robotsrulz/SP_Adapter/Inc/eeprom.h

/**
  ******************************************************************************
  * @file    EEPROM_Emulation/inc/eeprom.h 
  * @author  MCD Application Team
  * @version V1.6.0
  * @date    27-May-2016
  * @brief   This file contains all the functions prototypes for the EEPROM 
  *          emulation firmware library.
  ******************************************************************************
  * @attention
  *
  * <h2><center>&copy; COPYRIGHT(c) 2016 STMicroelectronics</center></h2>
  *
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
  ******************************************************************************
  */ 

/* Define to prevent recursive inclusion -------------------------------------*/
#ifndef __EEPROM_H
#define __EEPROM_H

/* Includes ------------------------------------------------------------------*/
#include "stm32f0xx_hal.h"

/* Exported constants --------------------------------------------------------*/

/* Base address of the Flash sectors */
#define ADDR_FLASH_PAGE_0     ((uint32_t)0x08000000) /* Base @ of Page 0, 2 Kbytes */
#define ADDR_FLASH_PAGE_1     ((uint32_t)0x08000800) /* Base @ of Page 1, 2 Kbytes */
#define ADDR_FLASH_PAGE_2     ((uint32_t)0x08001000) /* Base @ of Page 2, 2 Kbytes */
#define ADDR_FLASH_PAGE_3     ((uint32_t)0x08001800) /* Base @ of Page 3, 2 Kbytes */
#define ADDR_FLASH_PAGE_4     ((uint32_t)0x08002000) /* Base @ of Page 4, 2 Kbytes */
#define ADDR_FLASH_PAGE_5     ((uint32_t)0x08002800) /* Base @ of Page 5, 2 Kbytes */
#define ADDR_FLASH_PAGE_6     ((uint32_t)0x08003000) /* Base @ of Page 6, 2 Kbytes */
#define ADDR_FLASH_PAGE_7     ((uint32_t)0x08003800) /* Base @ of Page 7, 2 Kbytes */
#define ADDR_FLASH_PAGE_8     ((uint32_t)0x08004000) /* Base @ of Page 8, 2 Kbytes */
#define ADDR_FLASH_PAGE_9     ((uint32_t)0x08004800) /* Base @ of Page 9, 2 Kbytes */
#define ADDR_FLASH_PAGE_10    ((uint32_t)0x08005000) /* Base @ of Page 10, 2 Kbytes */
#define ADDR_FLASH_PAGE_11    ((uint32_t)0x08005800) /* Base @ of Page 11, 2 Kbytes */
#define ADDR_FLASH_PAGE_12    ((uint32_t)0x08006000) /* Base @ of Page 12, 2 Kbytes */
#define ADDR_FLASH_PAGE_13    ((uint32_t)0x08006800) /* Base @ of Page 13, 2 Kbytes */
#define ADDR_FLASH_PAGE_14    ((uint32_t)0x08007000) /* Base @ of Page 14, 2 Kbytes */
#define ADDR_FLASH_PAGE_15    ((uint32_t)0x08007800) /* Base @ of Page 15, 2 Kbytes */
#define ADDR_FLASH_PAGE_16    ((uint32_t)0x08008000) /* Base @ of Page 16, 2 Kbytes */
#define ADDR_FLASH_PAGE_17    ((uint32_t)0x08008800) /* Base @ of Page 17, 2 Kbytes */
#define ADDR_FLASH_PAGE_18    ((uint32_t)0x08009000) /* Base @ of Page 18, 2 Kbytes */
#define ADDR_FLASH_PAGE_19    ((uint32_t)0x08009800) /* Base @ of Page 19, 2 Kbytes */
#define ADDR_FLASH_PAGE_20    ((uint32_t)0x0800A000) /* Base @ of Page 20, 2 Kbytes */
#define ADDR_FLASH_PAGE_21    ((uint32_t)0x0800A800) /* Base @ of Page 21, 2 Kbytes */
#define ADDR_FLASH_PAGE_22    ((uint32_t)0x0800B000) /* Base @ of Page 22, 2 Kbytes */
#define ADDR_FLASH_PAGE_23    ((uint32_t)0x0800B800) /* Base @ of Page 23, 2 Kbytes */
#define ADDR_FLASH_PAGE_24    ((uint32_t)0x0800C000) /* Base @ of Page 24, 2 Kbytes */
#define ADDR_FLASH_PAGE_25    ((uint32_t)0x0800C800) /* Base @ of Page 25, 2 Kbytes */
#define ADDR_FLASH_PAGE_26    ((uint32_t)0x0800D000) /* Base @ of Page 26, 2 Kbytes */
#define ADDR_FLASH_PAGE_27    ((uint32_t)0x0800D800) /* Base @ of Page 27, 2 Kbytes */
#define ADDR_FLASH_PAGE_28    ((uint32_t)0x0800E000) /* Base @ of Page 28, 2 Kbytes */
#define ADDR_FLASH_PAGE_29    ((uint32_t)0x0800E800) /* Base @ of Page 29, 2 Kbytes */
#define ADDR_FLASH_PAGE_30    ((uint32_t)0x0800F000) /* Base @ of Page 30, 2 Kbytes */
#define ADDR_FLASH_PAGE_31    ((uint32_t)0x0800F800) /* Base @ of Page 31, 2 Kbytes */
#define ADDR_FLASH_PAGE_32    ((uint32_t)0x08010000) /* Base @ of Page 32, 2 Kbytes */
#define ADDR_FLASH_PAGE_33    ((uint32_t)0x08010800) /* Base @ of Page 33, 2 Kbytes */
#define ADDR_FLASH_PAGE_34    ((uint32_t)0x08011000) /* Base @ of Page 34, 2 Kbytes */
#define ADDR_FLASH_PAGE_35    ((uint32_t)0x08011800) /* Base @ of Page 35, 2 Kbytes */
#define ADDR_FLASH_PAGE_36    ((uint32_t)0x08012000) /* Base @ of Page 36, 2 Kbytes */
#define ADDR_FLASH_PAGE_37    ((uint32_t)0x08012800) /* Base @ of Page 37, 2 Kbytes */
#define ADDR_FLASH_PAGE_38    ((uint32_t)0x08013000) /* Base @ of Page 38, 2 Kbytes */
#define ADDR_FLASH_PAGE_39    ((uint32_t)0x08013800) /* Base @ of Page 39, 2 Kbytes */
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
#define ADDR_FLASH_PAGE_88    ((uint32_t)0x0802C000) /* Base @ of Page 88, 2 Kbytes */
#define ADDR_FLASH_PAGE_89    ((uint32_t)0x0802C800) /* Base @ of Page 89, 2 Kbytes */
#define ADDR_FLASH_PAGE_90    ((uint32_t)0x0802D000) /* Base @ of Page 90, 2 Kbytes */
#define ADDR_FLASH_PAGE_91    ((uint32_t)0x0802D800) /* Base @ of Page 91, 2 Kbytes */
#define ADDR_FLASH_PAGE_92    ((uint32_t)0x0802E000) /* Base @ of Page 92, 2 Kbytes */
#define ADDR_FLASH_PAGE_93    ((uint32_t)0x0802E800) /* Base @ of Page 93, 2 Kbytes */
#define ADDR_FLASH_PAGE_94    ((uint32_t)0x0802F000) /* Base @ of Page 94, 2 Kbytes */
#define ADDR_FLASH_PAGE_95    ((uint32_t)0x0802F800) /* Base @ of Page 95, 2 Kbytes */
#define ADDR_FLASH_PAGE_96    ((uint32_t)0x08030000) /* Base @ of Page 96, 2 Kbytes */
#define ADDR_FLASH_PAGE_97    ((uint32_t)0x08030800) /* Base @ of Page 97, 2 Kbytes */
#define ADDR_FLASH_PAGE_98    ((uint32_t)0x08031000) /* Base @ of Page 98, 2 Kbytes */
#define ADDR_FLASH_PAGE_99    ((uint32_t)0x08031800) /* Base @ of Page 99, 2 Kbytes */
#define ADDR_FLASH_PAGE_100   ((uint32_t)0x08032000) /* Base @ of Page 100, 2 Kbytes */
#define ADDR_FLASH_PAGE_101   ((uint32_t)0x08032800) /* Base @ of Page 101, 2 Kbytes */
#define ADDR_FLASH_PAGE_102   ((uint32_t)0x08033000) /* Base @ of Page 102, 2 Kbytes */
#define ADDR_FLASH_PAGE_103   ((uint32_t)0x08033800) /* Base @ of Page 103, 2 Kbytes */
#define ADDR_FLASH_PAGE_104   ((uint32_t)0x08034000) /* Base @ of Page 104, 2 Kbytes */
#define ADDR_FLASH_PAGE_105   ((uint32_t)0x08034800) /* Base @ of Page 105, 2 Kbytes */
#define ADDR_FLASH_PAGE_106   ((uint32_t)0x08035000) /* Base @ of Page 106, 2 Kbytes */
#define ADDR_FLASH_PAGE_107   ((uint32_t)0x08035800) /* Base @ of Page 107, 2 Kbytes */
#define ADDR_FLASH_PAGE_108   ((uint32_t)0x08036000) /* Base @ of Page 108, 2 Kbytes */
#define ADDR_FLASH_PAGE_109   ((uint32_t)0x08036800) /* Base @ of Page 109, 2 Kbytes */
#define ADDR_FLASH_PAGE_110   ((uint32_t)0x08037000) /* Base @ of Page 110, 2 Kbytes */
#define ADDR_FLASH_PAGE_111   ((uint32_t)0x08037800) /* Base @ of Page 111, 2 Kbytes */
#define ADDR_FLASH_PAGE_112   ((uint32_t)0x08038000) /* Base @ of Page 112, 2 Kbytes */
#define ADDR_FLASH_PAGE_113   ((uint32_t)0x08038800) /* Base @ of Page 113, 2 Kbytes */
#define ADDR_FLASH_PAGE_114   ((uint32_t)0x08039000) /* Base @ of Page 114, 2 Kbytes */
#define ADDR_FLASH_PAGE_115   ((uint32_t)0x08039800) /* Base @ of Page 115, 2 Kbytes */
#define ADDR_FLASH_PAGE_116   ((uint32_t)0x0803A000) /* Base @ of Page 116, 2 Kbytes */
#define ADDR_FLASH_PAGE_117   ((uint32_t)0x0803A800) /* Base @ of Page 117, 2 Kbytes */
#define ADDR_FLASH_PAGE_118   ((uint32_t)0x0803B000) /* Base @ of Page 118, 2 Kbytes */
#define ADDR_FLASH_PAGE_119   ((uint32_t)0x0803B800) /* Base @ of Page 119, 2 Kbytes */
#define ADDR_FLASH_PAGE_120   ((uint32_t)0x0803C000) /* Base @ of Page 120, 2 Kbytes */
#define ADDR_FLASH_PAGE_121   ((uint32_t)0x0803C800) /* Base @ of Page 121, 2 Kbytes */
#define ADDR_FLASH_PAGE_122   ((uint32_t)0x0803D000) /* Base @ of Page 122, 2 Kbytes */
#define ADDR_FLASH_PAGE_123   ((uint32_t)0x0803D800) /* Base @ of Page 123, 2 Kbytes */
#define ADDR_FLASH_PAGE_124   ((uint32_t)0x0803E000) /* Base @ of Page 124, 2 Kbytes */
#define ADDR_FLASH_PAGE_125   ((uint32_t)0x0803E800) /* Base @ of Page 125, 2 Kbytes */
#define ADDR_FLASH_PAGE_126   ((uint32_t)0x0803F000) /* Base @ of Page 126, 2 Kbytes */
#define ADDR_FLASH_PAGE_127   ((uint32_t)0x0803F800) /* Base @ of Page 127, 2 Kbytes */

/* Define the size of the sectors to be used */
#define PAGE_SIZE               (uint32_t)FLASH_PAGE_SIZE  /* Page size */

/* EEPROM start address in Flash */
#define EEPROM_START_ADDRESS  ((uint32_t)ADDR_FLASH_PAGE_14) /* EEPROM emulation start address */

/* Pages 0 and 1 base and end addresses */
#define PAGE0_BASE_ADDRESS    ((uint32_t)(EEPROM_START_ADDRESS + 0x0000))
#define PAGE0_END_ADDRESS     ((uint32_t)(EEPROM_START_ADDRESS + (PAGE_SIZE - 1)))

#define PAGE1_BASE_ADDRESS    ((uint32_t)(ADDR_FLASH_PAGE_15))
#define PAGE1_END_ADDRESS     ((uint32_t)(ADDR_FLASH_PAGE_15 + PAGE_SIZE - 1))

/* Used Flash pages for EEPROM emulation */
#define PAGE0                 ((uint16_t)0x0000)
#define PAGE1                 ((uint16_t)32) /* Page nb between PAGE0_BASE_ADDRESS & PAGE1_BASE_ADDRESS*/

/* No valid page define */
#define NO_VALID_PAGE         ((uint16_t)0x00AB)

/* Page status definitions */
#define ERASED                ((uint16_t)0xFFFF)     /* Page is empty */
#define RECEIVE_DATA          ((uint16_t)0xEEEE)     /* Page is marked to receive data */
#define VALID_PAGE            ((uint16_t)0x0000)     /* Page containing valid data */

/* Valid pages in read and write defines */
#define READ_FROM_VALID_PAGE  ((uint8_t)0x00)
#define WRITE_IN_VALID_PAGE   ((uint8_t)0x01)

/* Page full define */
#define PAGE_FULL             ((uint8_t)0x80)

/* Variables' number */
#define NB_OF_VAR             ((uint8_t)0x04)

/* Exported types ------------------------------------------------------------*/
/* Exported macro ------------------------------------------------------------*/
/* Exported functions ------------------------------------------------------- */
uint16_t EE_Init(void);
uint16_t EE_ReadVariable(uint16_t VirtAddress, uint16_t* Data);
uint16_t EE_WriteVariable(uint16_t VirtAddress, uint16_t Data);

#endif /* __EEPROM_H */

/************************ (C) COPYRIGHT STMicroelectronics *****END OF FILE****/
