robotsrulz/SP_Adapter/SP_Profiler/SP_Profiler.cpp

// SP_Profiler.cpp : Определяет поведение классов для приложения.
//

#include "stdafx.h"
#include "SP_Profiler.h"
#include "SP_ProfilerDlg.h"

#ifdef _DEBUG
#define new DEBUG_NEW
#endif


// CSP_ProfilerApp

BEGIN_MESSAGE_MAP(CSP_ProfilerApp, CWinApp)
	ON_COMMAND(ID_HELP, &CWinApp::OnHelp)
END_MESSAGE_MAP()


// создание CSP_ProfilerApp

CSP_ProfilerApp::CSP_ProfilerApp()
{
	// TODO: добавьте код создания,
	// Размещает весь важный код инициализации в InitInstance
}


// Единственный объект CSP_ProfilerApp

CSP_ProfilerApp theApp;


// инициализация CSP_ProfilerApp

BOOL CSP_ProfilerApp::InitInstance()
{
	// InitCommonControlsEx() требуется для Windows XP, если манифест
	// приложения использует ComCtl32.dll версии 6 или более поздней версии для включения
	// стилей отображения.  В противном случае будет возникать сбой при создании любого окна.
	INITCOMMONCONTROLSEX InitCtrls;
	InitCtrls.dwSize = sizeof(InitCtrls);
	// Выберите этот параметр для включения всех общих классов управления, которые необходимо использовать
	// в вашем приложении.
	InitCtrls.dwICC = ICC_WIN95_CLASSES;
	InitCommonControlsEx(&InitCtrls);

	CWinApp::InitInstance();


	// Создать диспетчер оболочки, в случае, если диалоговое окно содержит
	// представление дерева оболочки или какие-либо его элементы управления.
	CShellManager *pShellManager = new CShellManager;

	// Активация визуального диспетчера "Классический Windows" для включения элементов управления MFC
	CMFCVisualManager::SetDefaultManager(RUNTIME_CLASS(CMFCVisualManagerWindows));

	// Стандартная инициализация
	// Если эти возможности не используются и необходимо уменьшить размер
	// конечного исполняемого файла, необходимо удалить из следующих
	// конкретных процедур инициализации, которые не требуются
	// Измените раздел реестра, в котором хранятся параметры
	// TODO: следует изменить эту строку на что-нибудь подходящее,
	// например на название организации
	SetRegistryKey(_T("Локальные приложения, созданные с помощью мастера приложений"));

	CSP_ProfilerDlg dlg;
	m_pMainWnd = &dlg;
	INT_PTR nResponse = dlg.DoModal();
	if (nResponse == IDOK)
	{
		// TODO: Введите код для обработки закрытия диалогового окна
		//  с помощью кнопки "ОК"
	}
	else if (nResponse == IDCANCEL)
	{
		// TODO: Введите код для обработки закрытия диалогового окна
		//  с помощью кнопки "Отмена"
	}
	else if (nResponse == -1)
	{
		TRACE(traceAppMsg, 0, "Предупреждение. Не удалось создать диалоговое окно, поэтому работа приложения неожиданно завершена.\n");
		TRACE(traceAppMsg, 0, "Предупреждение. При использовании элементов управления MFC для диалогового окна невозможно #define _AFX_NO_MFC_CONTROLS_IN_DIALOGS.\n");
	}

	// Удалить диспетчер оболочки, созданный выше.
	if (pShellManager != NULL)
	{
		delete pShellManager;
	}

#ifndef _AFXDLL
	ControlBarCleanUp();
#endif

	// Поскольку диалоговое окно закрыто, возвратите значение FALSE, чтобы можно было выйти из
	//  приложения вместо запуска генератора сообщений приложения.
	return FALSE;
}
