robotsrulz/SP_Adapter/SP_Profiler/SP_ReportDlg.h

#pragma once


// диалоговое окно CSP_ReportDlg

class CSP_ReportDlg : public CDialogEx
{
	DECLARE_DYNAMIC(CSP_ReportDlg)

public:
	CSP_ReportDlg(CWnd* pParent = NULL);   // стандартный конструктор
	virtual ~CSP_ReportDlg();

	void addPoint(int x, int y);

// Данные диалогового окна
#ifdef AFX_DESIGN_TIME
	enum { IDD = IDD_REPORT_VIEW };
#endif

protected:
	afx_msg void OnPaint();

	virtual void DoDataExchange(CDataExchange* pDX);    // поддержка DDX/DDV

	DECLARE_MESSAGE_MAP()
};
