robotsrulz/SP_Adapter/SP_Profiler/resource.h

//{{NO_DEPENDENCIES}}
// Включаемый файл, созданный в Microsoft Visual C++.
// Используется SP_Profiler.rc
//
#define IDD_REPORTVIEW                  101
#define IDD_REPORT_VIEW                 101
#define IDD_SP_PROFILER_DIALOG          102
#define IDR_MAINFRAME                   128
#define IDC_COMBO1                      1002
#define IDC_HID_TARGETS                 1002
#define IDC_EDIT1                       1003
#define IDC_X_LOW_TH                    1003
#define IDC_EDIT2                       1004
#define IDC_X_HIGH_TH                   1004
#define IDC_EDIT3                       1005
#define IDC_Y_HIGH_TH                   1005
#define IDC_EDIT4                       1006
#define IDC_Y_LOW_TH                    1006
#define IDC_CUSTOM1                     1007
#define IDC_EDIT5                       1008
#define IDC_GEAR                        1008
#define ID_UPDATE                       1009
#define IDC_DRAW_FRAME                  1010
#define IDC_TARGETS_CTRL                1011
#define IDC_READ                        1012
#define IDC_VID                         1013
#define IDC_PID                         1014
#define IDC_VERSION                     1015
#define IDC_X                           1016
#define IDC_Y                           1017

// Next default values for new objects
// 
#ifdef APSTUDIO_INVOKED
#ifndef APSTUDIO_READONLY_SYMBOLS
#define _APS_NEXT_RESOURCE_VALUE        132
#define _APS_NEXT_COMMAND_VALUE         32771
#define _APS_NEXT_CONTROL_VALUE         1018
#define _APS_NEXT_SYMED_VALUE           101
#endif
#endif
