robotsrulz/SP_Adapter/SP_Profiler/stdafx.cpp

// stdafx.cpp: исходный файл, содержащий стандарт, включающий
// SP_Profiler.pch будет предварительно откомпилированным заголовком
// stdafx.obj будет содержать предварительно откомпилированные сведения о типе

#include "stdafx.h"
