robotsrulz/SP_Adapter/SP_Profiler/targetver.h

#pragma once

// Включение SDKDDKVer.h обеспечивает определение самой последней доступной платформы Windows.

// Если требуется выполнить сборку приложения для предыдущей версии Windows, включите WinSDKVer.h и
// задайте для макроопределения _WIN32_WINNT значение поддерживаемой платформы перед вхождением SDKDDKVer.h.

#include <SDKDDKVer.h>
